pdropes/Display-Brother/Photos/Teste de peças.jpg

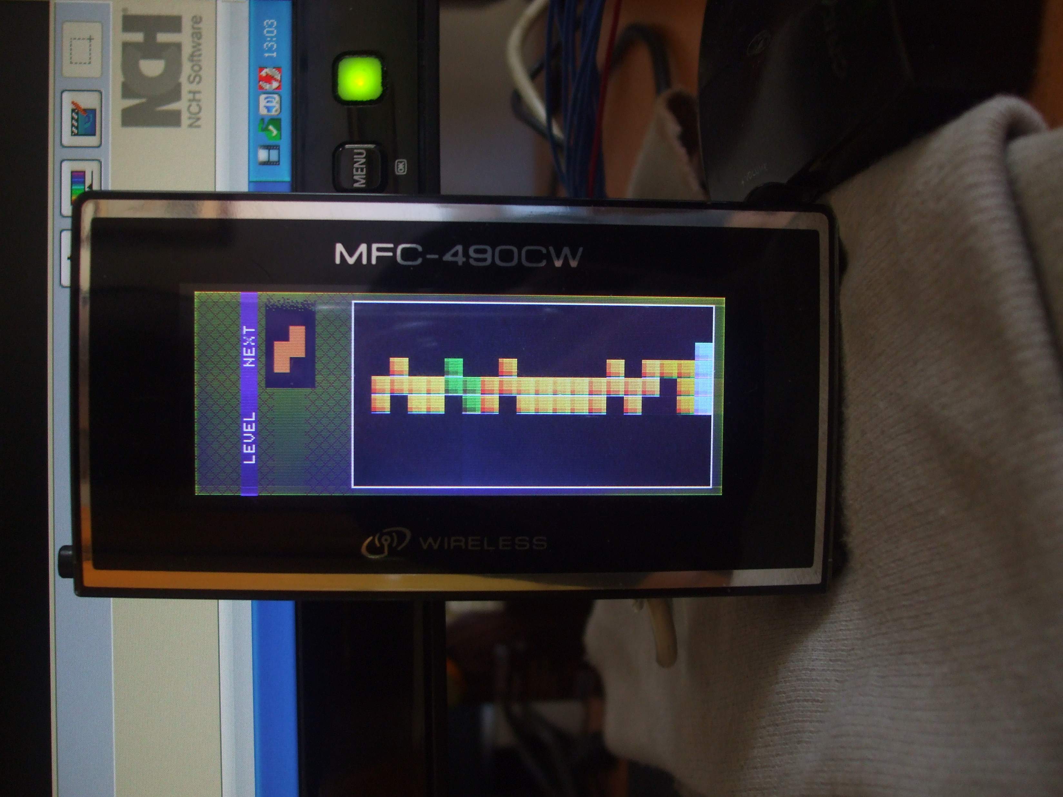
Photos/Teste de peças.jpg
