pdropes/Display-Brother/Source/Logo.bas

Logo:
Data &H00 , &H00 , &H00 , &H00 , &H00 , &H00 , &H00 , &H00 , &H00 , &H00 , &H00 , &H00 , &H00 , &H00 , &H00 , &H00 , &H00 , &H00 , &H00 , &H00 , &H00 , &H00 , &H00 , &H00 , &H00 , &H00 , &H00 , &H00 , &H00 , &H00 , &H00 , &H00 , &H00 , &H00 , &H00 , &H00 , &H00 , &H00 , &H00 , &H00 , &H00 , &H00 , &H00 , &H00 , &H00 , &H00 , &H00 , &H00 , &H00 , &H00 , &H00 , &H00 , &H00 , &H00 , &H00 , &H00 , &H00 , &H00 , &H00 , &H00 , &H00 , &H00 , &H00 , &H00 , &H00 , &H00 , &H00 , &H00 , &H00 , &H00 , &H00 , &H00 , &H00 , &H00 , &H00 , &H00 , &H00 , &H00 , &H00 , &H00 , &H00 , &H00 , &H00 , &H00 , &H00 , &H00 , &H00 , &H00 , &H00 , &H00 , &H00 , &H00 , &H00 , &H00 , &H00 , &H00 , &H00 , &H00 , &H00 , &H00 , &H00 , &H00 , &H00 , &H00 , &H00 , &H00 , &H00 , &H00 , &H00 , &H00 , &H00 , &H00 , &H00 , &H00 , &H00 , &H00 , &H00 , &H00 , &H00 , &H00 , &H00 , &H00 , &H00 , &H00 , &H00 , &H00 , &H00 , &H00 , &H00 , &H00 , &H00 , &H00
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
Data &H00 , &H00 , &H00 , &H00 , &H00 , &H00 , &H00 , &H00 , &H00 , &H00 , &H00 , &H00 , &H00 , &H00 , &H00 , &H00 , &H00 , &H00 , &H00 , &H00 , &H00 , &H00 , &H00 , &H00 , &H00 , &H00 , &H00 , &H00 , &H00 , &H00 , &H00 , &H00 , &H00 , &H00 , &H00 , &H00 , &H00 , &H00 , &H00 , &H00 , &H00 , &H00 , &H00 , &H00 , &H00 , &H00 , &H00 , &H00 , &H00 , &H00 , &H00 , &H00 , &H00 , &H00 , &H00 , &H00 , &H00 , &H00 , &H00 , &H00 , &H00 , &H00 , &H00 , &H00 , &H00 , &H00 , &H00 , &H00 , &H00 , &H00 , &H00 , &H00 , &H00 , &H00 , &H00 , &H00 , &H00 , &H00 , &H00 , &H00 , &H00 , &H00 , &H00 , &H00 , &H00 , &H00 , &H00 , &H00 , &H00 , &H00 , &H00 , &H00 , &H00 , &H00 , &H00 , &H00 , &H00 , &H00 , &H00 , &H00 , &H00 , &H00 , &H00 , &H00 , &H00 , &H00 , &H00 , &H00 , &H00 , &H00 , &H00 , &H00 , &H00 , &H00 , &H00 , &H00 , &H00 , &H00 , &H00 , &H00 , &H00 , &H00 , &H00 , &H00 , &H00 , &H00 , &H00 , &H00 , &H00 , &H00 , &H00 , &H00
